msommerx/Picframe/pictures/IMG_2581.jpg

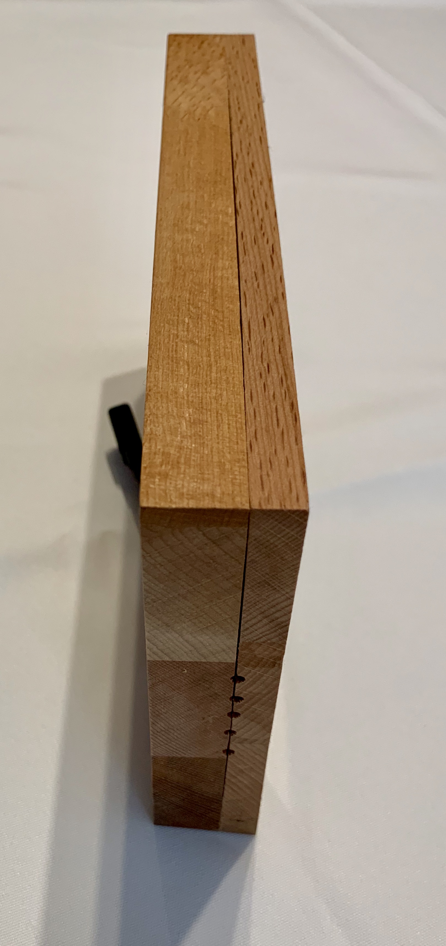
pictures/IMG_2581.jpg
