msommerx/Picframe/pictures/IMG_2583.jpg

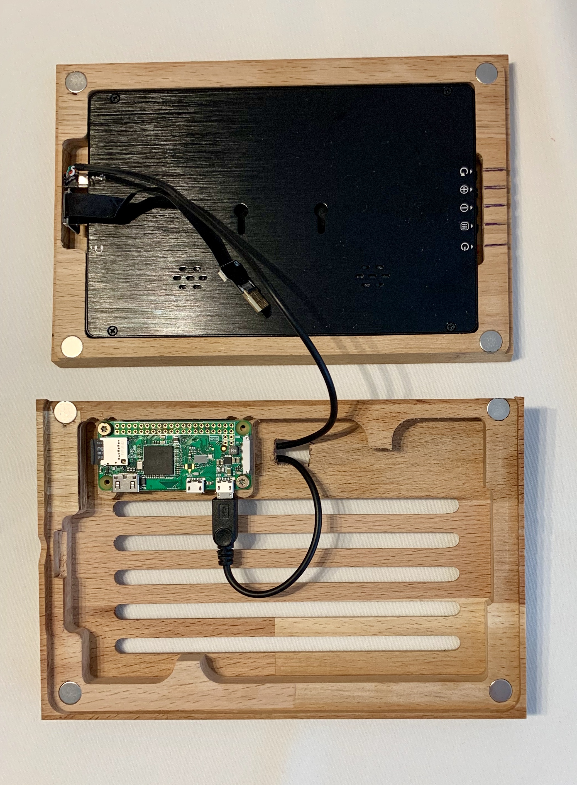
pictures/IMG_2583.jpg
